diGlitch/PimpMyPiano/scr/PimpMyPiano/src/PianoKey.cpp

/*
<PimpMyPiano - Mbed based interface between a Fatar TP44GH keybed and the midi world.>
Copyright (C) 2018  Jeremy Constantin Börker aka diGlitch

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
You should have received a copy of the GNU General Public License
along with this program.  If not, see <https://www.gnu.org/licenses/>.
*/

#include "PianoKey.h"
#include <stdlib.h> 

extern Serial pc;
extern MIDI midi;

const int MIN_DURATION = 3.0; // in ms
const int MAX_DURATION = 300.0; // in ms

#define DEBUG 0

PianoKey::PianoKey(int _midiNote)
{
    midiNote = _midiNote;
    timer.start();
    stateBR = false; //State for mk5
    stateMK = false; //State for br5
    sendNoteOff = false;
    timeMK = -1;
    timeBR = -1;
}

// Velocity courves
// velo1 - linear

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
int velo6 [(MAX_DURATION - MIN_DURATION)+1] = {127, 119, 116, 113, 111, 109, 107, 105, 103, 102, 100, 99, 98, 96, 95, 94, 93, 91, 90, 89, 88, 87, 86, 85, 84, 83, 82, 81, 80, 79, 78, 77, 77, 76, 75, 74, 73, 72, 72, 71, 70, 69, 69, 68, 67, 66, 66, 65, 64, 64, 63, 62, 62, 61, 61, 60, 59, 59, 58, 57, 57, 56, 56, 55, 55, 54, 54, 53, 52, 52, 51, 51, 50, 50, 49, 49, 48, 48, 47, 47, 47, 46, 46, 45, 45, 44, 44, 43, 43, 43, 42, 42, 41, 41, 41, 40, 40, 39, 39, 39, 38, 38, 38, 37, 37, 36, 36, 36, 35, 35, 35, 34, 34, 34, 33, 33, 33, 33, 32, 32, 32, 31, 31, 31, 30, 30, 30, 30, 29, 29, 29, 29, 28, 28, 28, 28, 27, 27, 27, 27, 26, 26, 26, 26, 25, 25, 25, 25, 24, 24, 24, 24, 24, 23, 23, 23, 23, 23, 22, 22, 22, 22, 22, 21, 21, 21, 21, 21, 20, 20, 20, 20, 20, 20, 19, 19, 19, 19, 19, 19, 18, 18, 18, 18, 18, 18, 17, 17, 17, 17, 17, 17, 16, 16, 16, 16, 16, 16, 16, 15, 15, 15, 15, 15, 15, 15, 14, 14, 14, 14, 14, 14, 13, 13, 13, 13, 13, 13, 13, 13, 12, 12, 12, 12, 12, 12, 12, 11, 11, 11, 11, 11, 11, 11, 10, 10, 10, 10, 10, 10, 10, 9, 9, 9, 9, 9, 9, 9, 8, 8, 8, 8, 8, 8, 8, 7, 7, 7, 7, 7, 7, 6, 6, 6, 6, 6, 6, 5, 5, 5, 5, 5, 5, 4, 4, 4, 4, 4, 4, 3, 3, 3, 3, 3, 3, 2, 2, 2, 2, 2, 1, 1, 1, 1, 1, 0, 0, 0};

// Adapted from processing.org map method
int PianoKey::getVelocity(int x)
{
    if (x > MAX_DURATION) {
        x = MAX_DURATION;
    }
#if DEBUG == 1
    printf("Velocity: %d with ", velo3[x-3]);
    printf(" %d ms\n", x);
#endif
    return velo6[x];
}

void PianoKey::resetMeasurement()
{
    timer.reset();
    timeMK = -1;
    timeBR = -1;
}

void PianoKey::SendNoteOn() {
    if (stateBR && stateMK) {
        int velo = getVelocity(abs(timeMK - timeBR));
        midi.sendNoteOn(midiNote, velo, 1);
#if DEBUG == 1
        printf("Send a note! :) \n");
        printf("-------------------\n");
        printf("time MK: %d \n", timeMK);
        printf("time BR: %d \n", timeBR);
        printf("difference: %d \n", timeBR-timeMK);
        printf("difference: %d \n", abs(timeBR-timeMK)) ;
        printf("velocity: %d \n", velo);
        printf("-------------------\n");
#endif
    }
}

void PianoKey::SendNoteOff() {
    if (!stateBR && !stateMK) {
        midi.sendNoteOff(midiNote, 0, 1);
#if DEBUG == 1
        printf("Turn a note off! ): \n");
#endif
    }
}

// 1st
void PianoKey::brPressed()
{
    if (!stateBR) {
        timeBR = timer.read_ms();
        stateBR = true;
        //printf("BR PRESSED\n");
        SendNoteOn();
    }
}

void PianoKey::brReleased()
{
    if (stateBR) {
        stateBR = false;
        SendNoteOff();
        //printf("BR Released\n");
    }
}

//2nd
void PianoKey::mkPressed()
{
    if (!stateMK) {
        timeMK = timer.read_ms();
        stateMK = true;
        //printf("MK PRESSED\n");
        SendNoteOn();
    }
}

void PianoKey::mkReleased()
{
    if (stateMK) {
        stateMK = false;
        //printf("MK Released\n");
        SendNoteOff();
        resetMeasurement();
    }

}
